IOIO72/scad-spool-painting-turntable/20210424_095954.jpg

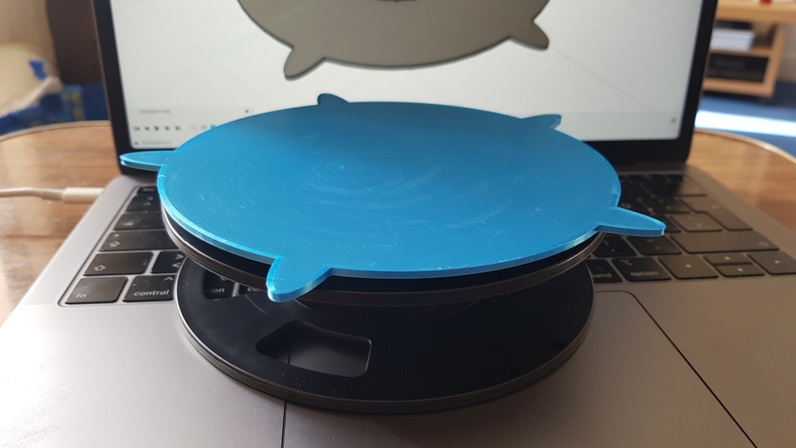
20210424_095954.jpg
